Technische-Natuurkunde-HvA/inverted-pendulum-international-team-6/data/Arduino_Connections_Pendulum.png

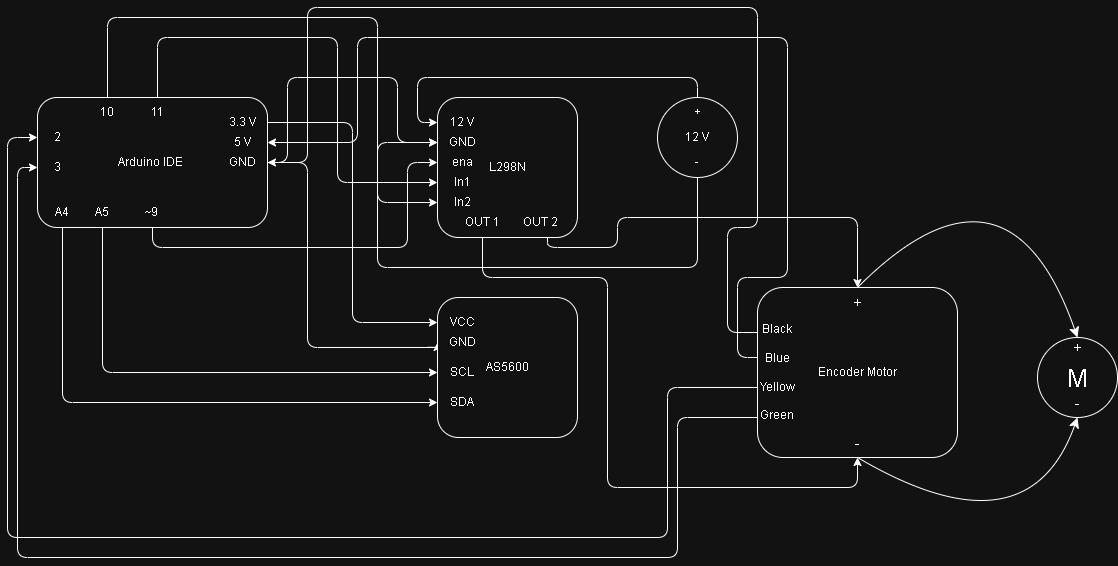
data/Arduino_Connections_Pendulum.png
