Technische-Natuurkunde-HvA/inverted-pendulum-international-team-6/data/AS5600_Angle_vs_Time.png

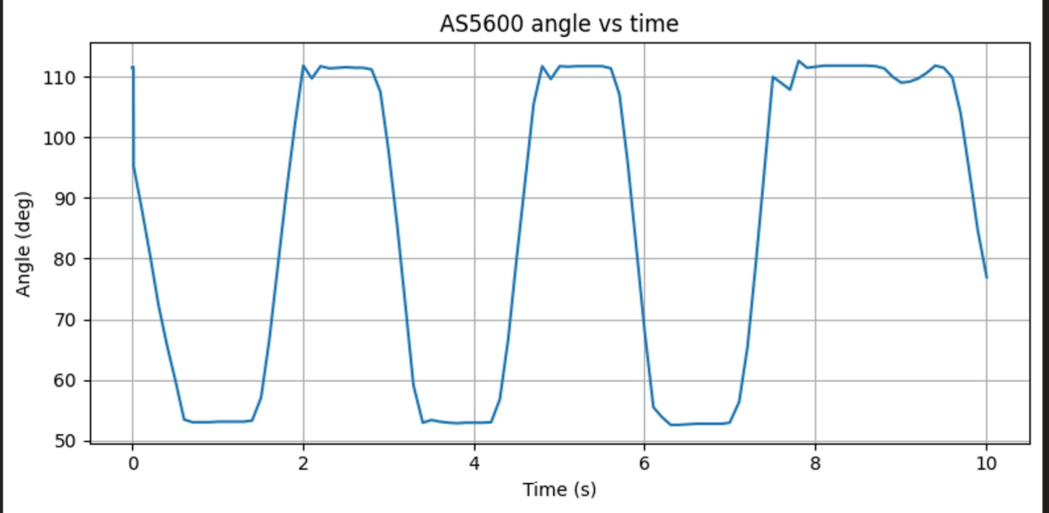
data/AS5600_Angle_vs_Time.png
